reinauer/amigahid-pico/src/display/disp_ssd.c

/**
 * ssd1306 display handling via i2c dma
 *
 * this code was very heavily inspired by https://github.com/fivdi/pico-i2c-dma; however, it was largely rewritten
 * as much of that code is considerate of multiple devices and uses freertos. this was chopped and replaced with an
 * interrupt-driven batch queue (though in truth nothing should race that hard that we ever need >1 operation in
 * flight, but is there for safety).
 *
 * @todo might be worth thinking about timeslicing the second cpu core: the mouse event loop will spend most of
 * its life sitting in delay & minimum signal interval to ensure the receiving system can handle the mouse motion
 * smoothly, so it's largely wasted. then this could be shifted to that core.
 */

#include "hardware/clocks.h"
#include "hardware/dma.h"
#include "hardware/gpio.h"
#include "hardware/i2c.h"
#include "hardware/irq.h"

#include <stdbool.h>
#include <stdint.h>
#include <stdlib.h>
#include <string.h>

#include "config.h"
#include "display/disp_ssd.h"
#include "display/ugui.h"

#define SSD_WIDTH           128
#define SSD_HEIGHT          64
#define SSD_BAUD            1000000         // 1MHz; if my estimation is correct, this could achieve 122fps
#define SSD_ADDR            0x3c            // my board has 0x78 jumper soldered closed on the back but ¯\_(ツ)_/¯
#define I2C_MAX_TRANSFER    0x400 + 0x20    // 1KB + 32B overhead
#define DISPLAY_QUEUE_LIMIT 64            // includes the startup command burst
#define DISPLAY_PROBE_TIMEOUT_US 25000

// display transaction structure
typedef struct
{
    uint8_t *write_buffer;
    size_t write_length;
    uint8_t *read_buffer;
    size_t read_length;

    void *next_transaction;
    void *prev_transaction;
} display_transaction_t;

static display_transaction_t *current_transaction = NULL,
                             *last_transaction = NULL,
                             *completed_transactions = NULL;

static uint8_t queue_depth = 0;
static bool display_failed = false;

/**
 * ssd1306 commands; borrowed from https://github.com/fivdi/pico-i2c-dma ssd1306 example code with thanks.
 * especially for the very comprehensive descriptions.
 */
typedef enum
{
    // Fundamental commands
    SET_CONTRAST = 0x81,         // Double byte command to select 1 out of
                                // 256 contrast steps.
    SET_ENTIRE_DISP_ON = 0xa4,   // Bit0 = 0: Output follows RAM content.
                                // Bit0 = 1: Output ignores RAM content,
                                //           all pixels are turned on.
    SET_NORMAL_INVERTED = 0xa6,  // Bit0 = 0: Normal display.
                                // Bit0 = 1: Inverted display.
    SET_DISP_ON_OFF = 0xae,      // Bit0 = 0: Display off, sleep mode.
                                // Bit0 = 1: Display on, normal mode.

    // Addressing setting Commands
    SET_ADDRESSING_MODE = 0x20,  // Double byte command to set memory
                                // addressing mode.
    SET_COLUMN_ADDRESS = 0x21,   // Triple byte command to setup column start
                                // and end address.
    SET_PAGE_ADDRESS = 0x22,     // Triple byte command to setup page start and
                                // end address.

    // Hardware configuration (panel resolution and layout related) commands
    SET_DISP_START_LINE = 0x40,  // Set display RAM display start line
                                // register. Valid values are 0 to 63.
    SET_SEGMENT_REMAP = 0xa0,    // Bit 0 = 0: Map col addr 0 to SEG0.
                                // Bit 0 = 1: Map col addr 127 to SEG0.
    SET_MUX_RATIO = 0xa8,        // Double byte command to configure display
                                // height. Valid height values are 15 to 63.
    SET_COM_OUTPUT_DIR = 0xc0,   // Bit 3 = 0: Scan from 0 to N-1.
                                // Bit 3 = 1: Scan from N-1 to 0. (N=height)
    SET_DISP_OFFSET = 0xd3,      // Double byte command to configure vertical
                                // display shift. Valid values are 0 to 63.
    SET_COM_PINS_CONFIG = 0xda,  // Double byte command to set COM pins
                                // hardware configuration.

    // Timing and driving scheme setting commands
    SET_DCLK_FOSC = 0xd5,        // Double byte command to set display clock
                                // divide ratio and oscillator frequency.
    SET_PRECHARGE_PERIOD = 0xd9, // Double byte command to set pre-charge
                                // period.
    SET_VCOM_DESEL_LEVEL = 0xdb, // Double byte command to set VCOMH deselect
                                // level.

    // Charge pump command
    SET_CHARGE_PUMP = 0x8d,      // Double byte command to enable/disable
                                // charge pump.
                                // Byte2 = 0x10: Disable charge pump.
                                // Byte2 = 0x14: Enable charge pump.
} ssd1306_command_t;

// The IRQ handler starts the next queued transaction.
static bool disp_i2c_init(void);
static void disp_i2c_trans(uint8_t *write_buffer, size_t write_length, uint8_t *read_buffer, size_t read_length);

// declare disp_write wrapper destinations for the pointer
void _noop_disp_write(uint8_t x, uint8_t y, char *message);
void _real_disp_write(uint8_t x, uint8_t y, char *message);

// i2c transfer flags: stop means "finished", abort means "something failed so i gave up"
static bool _stop = false,
            _abort = false,
            _reading = false,
            _writing = false;

// dma channels
static int tx_chan = -1,
           rx_chan = -1;

// display things: pixel command buffer (1 command followed by (x * y)/8)
static uint8_t display_command[1 + ((SSD_WIDTH * SSD_HEIGHT) / 8)];
// the above buffer has a write command (0x40) followed by the framebuffer; point to the start of the framebuffer
static uint8_t *framebuffer = &display_command[1];
// Keep status/pairing updates while a menu is visible or the display is blank.
static uint8_t status_framebuffer[(SSD_WIDTH * SSD_HEIGHT) / 8];
static bool menu_overlay;
static bool status_enabled = true;

// ugui's instance
static UG_GUI gui;

// convert from ugui's vernacular to a proper word
typedef UG_COLOR UG_COLOUR;

// point disp_write(...) at _real_disp_write(...); it'll point to _noop_disp_write(...) if init fails
void (*disp_write)(uint8_t x, uint8_t y, char *message) = _real_disp_write;

/**
 * Interrupt service routine for i2c device: is called on transaction abort or completion
 *
 * @return void
 */
static void disp_ssd_i2c_irqh(void)
{
    uint32_t status = i2c_get_hw(I2C_PORT)->intr_stat;

    // check for trans abort; read register causes clear to occur
    if (status & I2C_IC_INTR_STAT_R_TX_ABRT_BITS) {
        i2c_get_hw(I2C_PORT)->clr_tx_abrt;
        _abort = true;
    }

    // check for trans stop (complete); read register causes clear to occur
    if (status & I2C_IC_INTR_STAT_R_STOP_DET_BITS) {
        i2c_get_hw(I2C_PORT)->clr_stop_det;
        _stop = true;
    }

    if (current_transaction == NULL || (!_abort && !_stop))
        return;

    // A failed OLED must not block USB/Bluetooth in interrupt context. Stop
    // using it until reboot and leave all memory cleanup to the main loop.
    if (_abort) {
        i2c_get_hw(I2C_PORT)->intr_mask = 0;
        dma_channel_abort(tx_chan);
        if (_reading)
            dma_channel_abort(rx_chan);
        last_transaction->next_transaction = completed_transactions;
        completed_transactions = current_transaction;
        current_transaction = last_transaction = NULL;
        queue_depth = 0;
        display_failed = true;
        return;
    }

    display_transaction_t *finished = current_transaction;
    current_transaction = finished->next_transaction;
    finished->next_transaction = completed_transactions;
    completed_transactions = finished;
    queue_depth--;

    // trigger next transaction to start processing
    if (current_transaction != NULL) {
        disp_i2c_trans(
            current_transaction->write_buffer,
            current_transaction->write_length,
            current_transaction->read_buffer,
            current_transaction->read_length
        );
    } else {
        last_transaction = NULL;
    }
}

// Main-loop only: the allocator is not safe to interrupt with an ISR free().
static void disp_free_transaction(display_transaction_t *transaction)
{
    free(transaction->write_buffer);
    free(transaction->read_buffer);
    free(transaction);
}

void disp_ssd_task(void)
{
    uint irqn = (I2C_PORT == i2c0) ? I2C0_IRQ : I2C1_IRQ;
    bool enabled = irq_is_enabled(irqn);
    irq_set_enabled(irqn, false);
    display_transaction_t *finished = completed_transactions;
    completed_transactions = NULL;
    irq_set_enabled(irqn, enabled);

    while (finished != NULL) {
        display_transaction_t *next = finished->next_transaction;
        disp_free_transaction(finished);
        finished = next;
    }
}

/**
 * Set a pin to open drain
 *
 * @param uint pin  The pin to set open drain
 */
static void open_drain(uint pin)
{
    gpio_set_function(pin, GPIO_FUNC_SIO);
    gpio_set_dir(pin, GPIO_IN);
    gpio_put(pin, 0);
}

/**
 * Check if the i2c bus is signalling a blockage
 *
 * @return bool true if blocked, false if not
 */
static bool check_blocked(void)
{
    bool sda_lev, scl_lev;

    open_drain(I2C_PIN_SDA);
    open_drain(I2C_PIN_SCL);

    sda_lev = gpio_get(I2C_PIN_SDA);
    scl_lev = gpio_get(I2C_PIN_SCL);

    return !sda_lev || !scl_lev;
}

/**
 * Forcibly unblock the i2c bus by flip/flopping the clock line in and out
 *
 * @return void
 */
static void unblock(void)
{
    open_drain(I2C_PIN_SDA);
    open_drain(I2C_PIN_SCL);

    bool sda_lev = gpio_get(I2C_PIN_SDA);
    uint32_t delay_ct,
             tries,
             drain_delay = frequency_count_khz(CLOCKS_FC0_SRC_VALUE_CLK_SYS) / 200;

    // try to clear the bus 9 times; if it doesn't clear, meh, just carry on; it _might_ be ok
    for (tries = 0; (tries < 9) && !sda_lev; tries++) {
        // flip the clock between level & drain and re-check the sda line; when it's high, the bus is cleared
        gpio_set_dir(I2C_PIN_SCL, GPIO_OUT);
        for (delay_ct = 0; delay_ct < drain_delay; delay_ct++)
            __asm__("nop");

        gpio_set_dir(I2C_PIN_SCL, GPIO_IN);
        for (delay_ct = 0; delay_ct < drain_delay; delay_ct++)
            __asm__("nop");

        sda_lev = gpio_get(I2C_PIN_SDA);
    }
}

/**
 * Initialise the i2c controller, and set up the interrupt service routine
 *
 * @return bool true if successful, false if not present or an error occurred
 */
bool disp_i2c_init(void)
{
    // aaaand if, say, an rp2041 arrives with >2 i2c interfaces, this is where the breakage exists :D
    uint irqn = (I2C_PORT == i2c0) ? I2C0_IRQ : I2C1_IRQ;

    // disable isr whilst we're changing i2c settings
    irq_set_enabled(irqn, false);

    // since this is a fresh init, set these to false
    _abort = false;
    _stop = false;
    display_failed = false;

    // unblock bus, if it's blocked
    if (check_blocked())
        unblock();

    // init i2c interface, setup baud rate
    i2c_init(I2C_PORT, SSD_BAUD);

    // claim pins as i2c
    gpio_set_function(I2C_PIN_SDA, GPIO_FUNC_I2C);
    gpio_set_function(I2C_PIN_SCL, GPIO_FUNC_I2C);
    gpio_pull_up(I2C_PIN_SDA);
    gpio_pull_up(I2C_PIN_SCL);

    // check for presence of display in blocking mode before we do anything dma related
    uint8_t command[2] = {0x80, SET_DISP_ON_OFF | 0x00}; // tell display to turn off
    int result = i2c_write_timeout_us(I2C_PORT, SSD_ADDR, command, sizeof(command), false,
        DISPLAY_PROBE_TIMEOUT_US);
    if (result != sizeof(command)) {
        // no device present
        // @todo setup function pointers but point them at noops if we discover the device is not present here.
        //       that way we don't end up wasting cycles firing data indiscriminately at something not present.
        disp_write = _noop_disp_write;
        display_failed = true;
        return false;
    }
    disp_write = _real_disp_write;

    // set stop and abort interrupt flags
    i2c_get_hw(I2C_PORT)->intr_mask = I2C_IC_INTR_MASK_M_STOP_DET_BITS | I2C_IC_INTR_MASK_M_TX_ABRT_BITS;

    // activate the isr for the i2c interrupt
    irq_set_exclusive_handler(irqn, disp_ssd_i2c_irqh);

    // we might be reinitialising; free the channels if they're occupied otherwise we'll accidentally claim two more
    // without releasing the previous ones.
    if (tx_chan >= 0)
        dma_channel_unclaim(tx_chan);
    if (rx_chan >= 0)
        dma_channel_unclaim(rx_chan);

    // get some dma channels
    tx_chan = dma_claim_unused_channel(true);
    rx_chan = dma_claim_unused_channel(true);
    irq_set_enabled(irqn, true);

    return true;
}

/**
 * Configure a receive DMA channel for an i2c device and start the DMA operation.
 *
 * @param int rx_chan           DMA channel to use for receiving data
 * @param uint8_t *read_buffer  Address of uint8_t buffer to read data into
 * @param size_t read_length    Number of bytes to expect to read (DMA op will conclude once length reached or 'stop' received)
 * @return void
 */
static void configure_rx_channel(int rx_chan, uint8_t *read_buffer, size_t read_length)
{
    dma_channel_config rx_config = dma_channel_get_default_config(rx_chan);
    channel_config_set_read_increment(&rx_config, false);
    channel_config_set_write_increment(&rx_config, true);
    channel_config_set_transfer_data_size(&rx_config, DMA_SIZE_8);
    channel_config_set_dreq(&rx_config, i2c_get_dreq(I2C_PORT, false));
    dma_channel_configure(rx_chan, &rx_config, read_buffer, &i2c_get_hw(I2C_PORT)->data_cmd, read_length, true);
}

/**
 * Configure a transmit DMA channel for an i2c device and start the DMA operation.
 * Note: The write_buffer is uint16 encoded, as a pair of <i2c instruction><device instruction>, and the constants
 * for this can be found in "hardware/i2c.h" in the pico sdk.
 *
 * @param int tx_chan               DMA channel to use for transmission
 * @param uint16_t *write_buffer    Address of uint16_t buffer containing i2c/device instruction pairs
 * @param size_t write_length       Length of write buffer (in bytes, ergo one uint16_t = 2)
 * @return void
 */
static void configure_tx_channel(int tx_chan, uint16_t *write_buffer, size_t write_length)
{
    dma_channel_config tx_config = dma_channel_get_default_config(tx_chan);
    channel_config_set_read_increment(&tx_config, true);
    channel_config_set_write_increment(&tx_config, false);
    channel_config_set_transfer_data_size(&tx_config, DMA_SIZE_16);
    channel_config_set_dreq(&tx_config, i2c_get_dreq(I2C_PORT, true));
    dma_channel_configure(tx_chan, &tx_config, &i2c_get_hw(I2C_PORT)->data_cmd, write_buffer, write_length, true);
}

/**
 * Perform a read/write transaction to the i2c device
 *
 * @param uint8_t *write_buffer Location of the stream to write out
 * @param size_t write_length   Length of the stream to write
 * @param uint8_t *read_buffer  Location of the buffer to read back into
 * @param size_t read_length    Length of the stream to read
 * @return void
 */
static void disp_i2c_trans(uint8_t *write_buffer, size_t write_length, uint8_t *read_buffer, size_t read_length)
{
    // commands are sent as 16-bit transactions, including the i2c action (start/stop, 0 means just "carry on sending
    // until another instruction")
    static uint16_t data_commands[I2C_MAX_TRANSFER];

    if ((write_length + read_length) > I2C_MAX_TRANSFER)
        // cowardly refuse to go over maximum transfer size
        // @todo at some point, if this happens, log, complain, dequeue and continue
        panic(
            "disp_i2c_trans() exceeded maximum allowed buffer size (read: 0x%x, write: 0x%x, max: 0x%x)\n",
            read_length,
            write_length,
            I2C_MAX_TRANSFER
        );

    _writing = write_length > 0;
    _reading = read_length > 0;

    size_t pos;

    if (_writing) {
        for (pos = 0; pos != write_length; ++pos)
            data_commands[pos] = write_buffer[pos];

        data_commands[0] |= I2C_IC_DATA_CMD_RESTART_BITS;
    }

    if (_reading) {
        for (pos = 0; pos != read_length; ++pos)
            data_commands[write_length + pos] = I2C_IC_DATA_CMD_CMD_BITS;

        data_commands[write_length] |= I2C_IC_DATA_CMD_RESTART_BITS;
    }

    data_commands[write_length + read_length - 1] |= I2C_IC_DATA_CMD_STOP_BITS;

    i2c_get_hw(I2C_PORT)->enable = 0;
    i2c_get_hw(I2C_PORT)->tar = SSD_ADDR;
    i2c_get_hw(I2C_PORT)->enable = 1;

    _stop = false;
    _abort = false;

    // assign the dma channels and start the transfer
    if (_reading)
        configure_rx_channel(rx_chan, read_buffer, read_length);

    configure_tx_channel(tx_chan, data_commands, write_length + read_length);
}

/**
 * Queue an i2c transaction at the end of the transaction list; if no transaction is being processed, dispatch that
 * transaction immediately.
 *
 * @todo it became immediately apparent to me whilst writing that the transaction list methodology won't work for
 *       reading data. truth is, we're never going to read data from the display, so we probably don't need any
 *       of the read handling, so it can likely be removed.
 *
 * @param uint8_t *write_buffer Pointer of uint8_t buffer to write to the device
 * @param size_t write_length   Length of the write_buffer
 * @param uint8_t *read_buffer  Pointer of uint8_t buffer to read data into
 * @param size_t read_length    Length of data to put into the buffer
 * @return void
 */
void disp_queue_transaction(uint8_t *write_buffer, size_t write_length, uint8_t *read_buffer, size_t read_length)
{
    // Called only from core0's main context, including Bluetooth UI updates.
    disp_ssd_task();
    if (display_failed || queue_depth >= DISPLAY_QUEUE_LIMIT ||
        write_length > I2C_MAX_TRANSFER || read_length > I2C_MAX_TRANSFER - write_length ||
        (write_length == 0 && read_length == 0) ||
        (write_length > 0 && write_buffer == NULL) || (read_length > 0 && read_buffer == NULL))
        return;

    display_transaction_t *new_transaction = malloc(sizeof(display_transaction_t));
    if (new_transaction == NULL)
        return;
    new_transaction->write_buffer = NULL;
    new_transaction->write_length = write_length;
    new_transaction->read_buffer = NULL;
    new_transaction->read_length = read_length;
    new_transaction->next_transaction = NULL;

    uint irqn = (I2C_PORT == i2c0) ? I2C0_IRQ : I2C1_IRQ;

    if (write_length > 0) {
        new_transaction->write_buffer = malloc(write_length);
        if (new_transaction->write_buffer == NULL) {
            disp_free_transaction(new_transaction);
            return;
        }
        memcpy(new_transaction->write_buffer, write_buffer, write_length);
    }

    if (read_length > 0) {
        new_transaction->read_buffer = malloc(read_length);
        if (new_transaction->read_buffer == NULL) {
            disp_free_transaction(new_transaction);
            return;
        }
        memcpy(new_transaction->read_buffer, read_buffer, read_length);
    }

    // Mask before testing current_transaction: completion can otherwise remove
    // the last queue entry between the test and the append below.
    irq_set_enabled(irqn, false);
    if (display_failed) {
        irq_set_enabled(irqn, true);
        disp_free_transaction(new_transaction);
        return;
    }
    queue_depth++;

    // check if we're the the first item in the list and act accordingly
    if (current_transaction == NULL) {
        new_transaction->prev_transaction = NULL;
        last_transaction = current_transaction = new_transaction;

        disp_i2c_trans(
            new_transaction->write_buffer,
            new_transaction->write_length,
            new_transaction->read_buffer,
            new_transaction->read_length
        );

        irq_set_enabled(irqn, true);

        return;
    }

    // this is not the first item, so shove this on the end of the queue
    new_transaction->prev_transaction = last_transaction;
    last_transaction->next_transaction = new_transaction;
    last_transaction = new_transaction;
    irq_set_enabled(irqn, true);
}

/**
 * UGUI callback: Translate ugui pixel draw to the ssd1306 display buffer
 *
 * @param UG_S16 x      x position to draw to
 * @param UG_S16 y      y position to draw to
 * @param UG_S16 colour Colour of pixel
 * @return void
 */
static void ugui_draw_pixel_cb(UG_S16 x, UG_S16 y, UG_COLOUR colour)
{
    if ((x < 0) ||
        (x > (SSD_WIDTH - 1)) ||
        (y < 0) ||
        (y > (SSD_HEIGHT - 1))
    ) {
        // we don't want your mucky offscreen pixels here. what do you think this is, a snes?
        return;
    }

    uint8_t *byte = &framebuffer[((y / 8) * SSD_WIDTH) + x];
    uint8_t bitmask = 1 << (y % 8);

    switch (colour) {
        case C_BLACK:
            *byte &= ~bitmask; // clear pixel
            break;
        case C_WHITE:
            *byte |= bitmask; // set pixel
            break;
        default:
            *byte ^= bitmask; // invert pixel for anything else (should we just panic tho?)
    }
}

/**
 * Redraw the SSD1306 display
 *
 * @return void
 */
static void disp_ssd_update()
{
    disp_queue_transaction(display_command, sizeof(display_command), NULL, 0);
}

/**
 * In the case that i2c init fails, this is where disp_write is pointed
 */
void _noop_disp_write(uint8_t x, uint8_t y, char *message)
{
    __asm__("nop");
}

/**
 * Write a message to the display
 *
 * @param uint8_t x     x offset (in characters)
 * @param uint8_t y     y offset (in characters)
 * @return void
 */
void _real_disp_write(uint8_t x, uint8_t y, char *message)
{
    if (display_failed || y >= 4)
        return;
    UG_S16 px = x * 5,
           py = y * 14;

    framebuffer = status_framebuffer;
    UG_PutString(px, py, message);
    framebuffer = &display_command[1];
    if (!menu_overlay && status_enabled) {
        memcpy(framebuffer, status_framebuffer, sizeof(status_framebuffer));
        disp_ssd_update();
    }
}

// Keep the firmware identity visible below the four status/pairing lines.
// Like disp_write(), this must only be called from the main context.
void disp_ssd_version(char *version)
{
    if (display_failed)
        return;
    framebuffer = status_framebuffer;
    UG_FontSelect(&FONT_5X8);
    UG_PutString(0, 56, version);
    UG_FontSelect(&FONT_5X12);
    framebuffer = &display_command[1];
    if (!menu_overlay && status_enabled) {
        memcpy(framebuffer, status_framebuffer, sizeof(status_framebuffer));
        disp_ssd_update();
    }
}

bool disp_ssd_available(void)
{
    return !display_failed && disp_write == _real_disp_write;
}

static void restore_status(void)
{
    if (!disp_ssd_available() || menu_overlay)
        return;
    if (status_enabled)
        memcpy(framebuffer, status_framebuffer, sizeof(status_framebuffer));
    else
        memset(framebuffer, 0, sizeof(status_framebuffer));
    disp_ssd_update();
}

void disp_ssd_set_enabled(bool enabled)
{
    status_enabled = enabled;
    restore_status();
}

void disp_ssd_set_overlay(bool active)
{
    menu_overlay = active;
    restore_status();
}

void disp_ssd_menu(char const *heading, char const *item, char const *value, char const *hint)
{
    if (!disp_ssd_available() || !menu_overlay)
        return;
    char const *lines[] = {heading, item, value, hint};
    UG_FillScreen(C_BLACK);
    for (unsigned row = 0; row < 4; row++)
        UG_PutString(0, row * 14, (char *)lines[row]);
    // The last framebuffer page holds the firmware version at y=56..63.
    memcpy(framebuffer + SSD_WIDTH * 7, status_framebuffer + SSD_WIDTH * 7, SSD_WIDTH);
    disp_ssd_update();
}

/**
 * Write a byte to a register on the i2c device
 *
 * @param uint8_t devregister   Register to write to
 * @param uint8_t byte          Byte to write
 * @return void
 */
static inline void write_byte(uint8_t devregister, uint8_t byte)
{
    // write a byte to a register
    uint8_t buffer[2] = {devregister, byte};
    disp_queue_transaction(buffer, 2, NULL, 0);
}

/**
 * Setup the i2c and ssd1306 display ready for use. Without calling this, behaviour is undefined.
 *
 * @return void
 */
void disp_ssd_init(void)
{
    const uint8_t init_sequence[] = {
        SET_DISP_ON_OFF | 0x00,         // Display off.
        SET_DCLK_FOSC, 0x80,            // Set clock divide ratio and oscillator
                                        //   frequency.
        SET_MUX_RATIO, 0x3f,            // Set display height.
        SET_DISP_OFFSET, 0x00,          // Set vertical display shift to 0.
        SET_DISP_START_LINE,            // Set display RAM display start line
                                        //   register to 0.
        SET_CHARGE_PUMP, 0x14,          // Enable charge pump.
        SET_SEGMENT_REMAP | 0x01,       // Map col addr 127 to SEG0.
        SET_COM_OUTPUT_DIR | 0x08,      // Scan from N-1 to 0. (N=height)
        SET_COM_PINS_CONFIG, 0x12,      // Set COM pins hardware configuration to
                                        //   0x12.
        SET_CONTRAST, 0xcf,             // Set contrast to 0xcf
        SET_PRECHARGE_PERIOD, 0xf1,     // Set pre-charge to 0xf1
        SET_VCOM_DESEL_LEVEL, 0x40,     // Set VCOMH deselect to 0x40
        SET_ENTIRE_DISP_ON,             // Output follows RAM content.
        SET_NORMAL_INVERTED | 0x00,     // Normal display.
        SET_ADDRESSING_MODE, 0x00,      // Set addressing mode to horizontal mode.
        SET_COLUMN_ADDRESS, 0x00, 0x7f, // Set column start and end address.
        SET_PAGE_ADDRESS, 0x00, 0x07,   // Set page start and end address.
        SET_DISP_ON_OFF | 0x01,         // Display on.
    };

    // start the i2c device control
    if (disp_i2c_init() == false)
        return;

    // commands sent to the ssd1306 are written to a single location on register 0x80, and
    // as such cannot be sent as a block. even command parameters must be sent to the same
    // register, so it all has to go, one byte at a time, waiting for the isr to signal stop
    // after each byte.
    for (uint pos = 0; pos < sizeof(init_sequence); pos++)
        write_byte(0x80, init_sequence[pos]);

    // set the command at the beginning of the framebuffer to write out
    display_command[0] = SET_DISP_START_LINE;

    // setup ugui, blank the display
    UG_Init(&gui, ugui_draw_pixel_cb, SSD_WIDTH, SSD_HEIGHT);
    UG_SetBackcolor(C_BLACK);
    UG_SetForecolor(C_WHITE);
    UG_FillScreen(C_BLACK);
    UG_FontSelect(&FONT_5X12);
}
